sonatine726/zakojifarm_iotfieldsensor/Images/Products/1_8.PNG

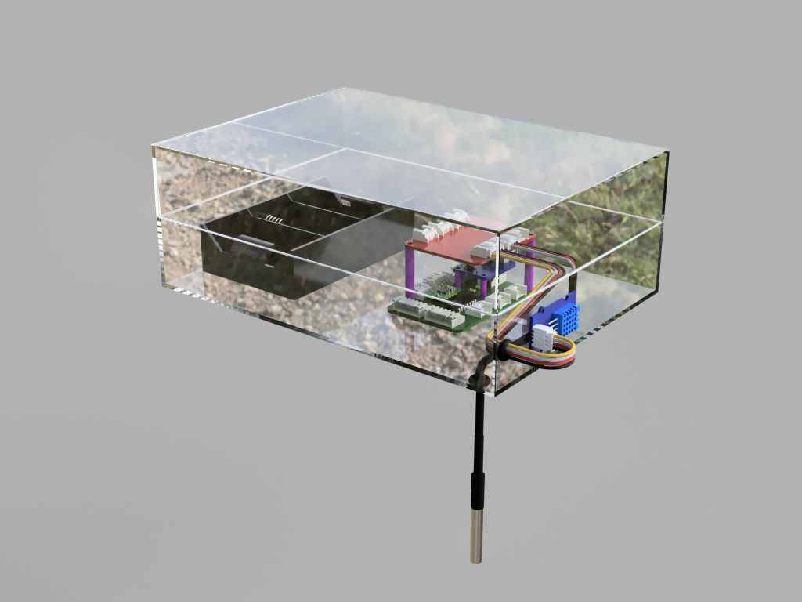
Images/Products/1_8.PNG
