sonatine726/zakojifarm_iotfieldsensor/Images/Products/2_6.PNG

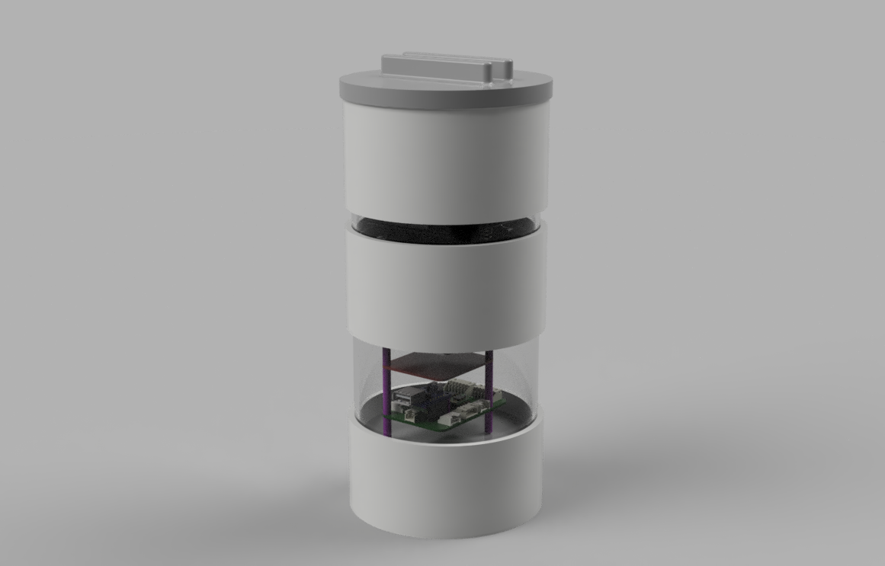
Images/Products/2_6.PNG
