sonatine726/zakojifarm_iotfieldsensor/Images/Products/2_9.jpg

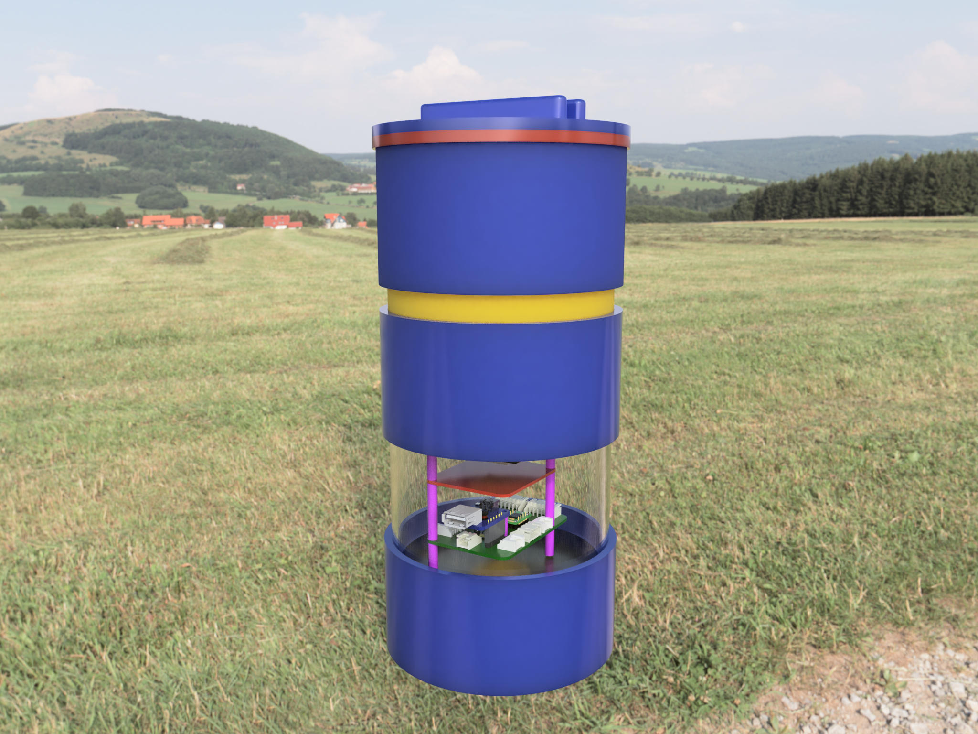
Images/Products/2_9.jpg
