sonatine726/zakojifarm_iotfieldsensor/Images/Products/4_1.PNG

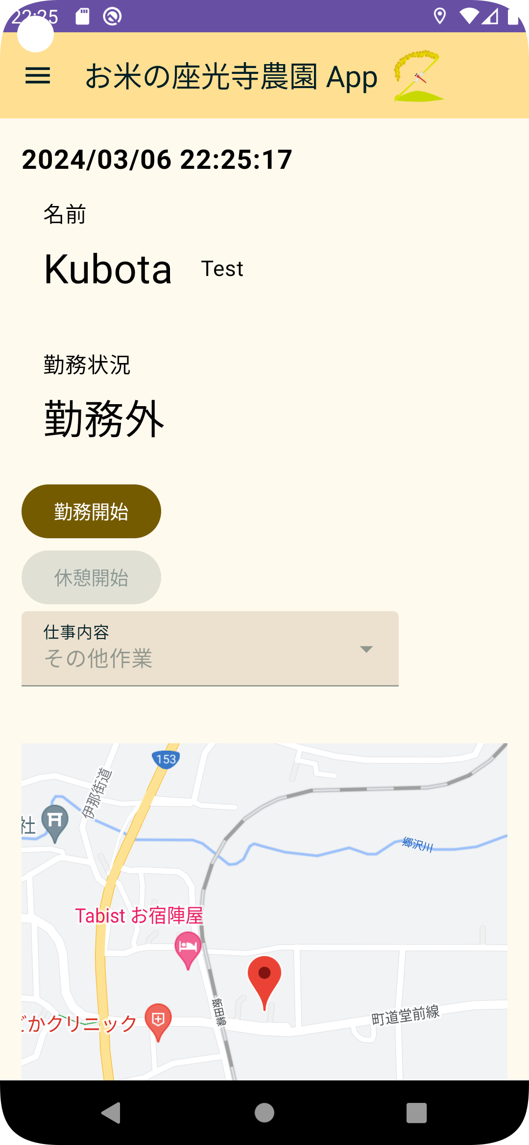
Images/Products/4_1.PNG
