sonatine726/zakojifarm_iotfieldsensor/Images/Products/4_2.PNG

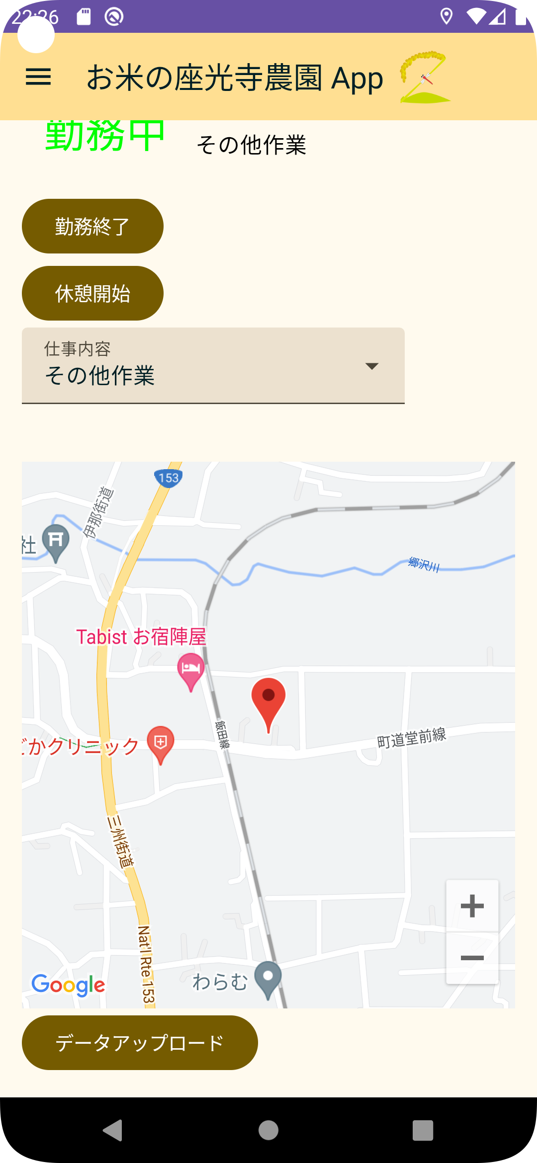
Images/Products/4_2.PNG
