sonatine726/zakojifarm_iotfieldsensor/Images/Products/5_1.jpg

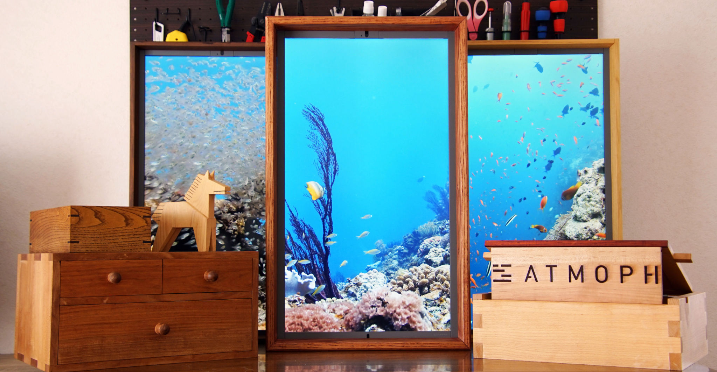
Images/Products/5_1.jpg
