sonatine726/zakojifarm_iotfieldsensor/Images/Products/5_2.jpg

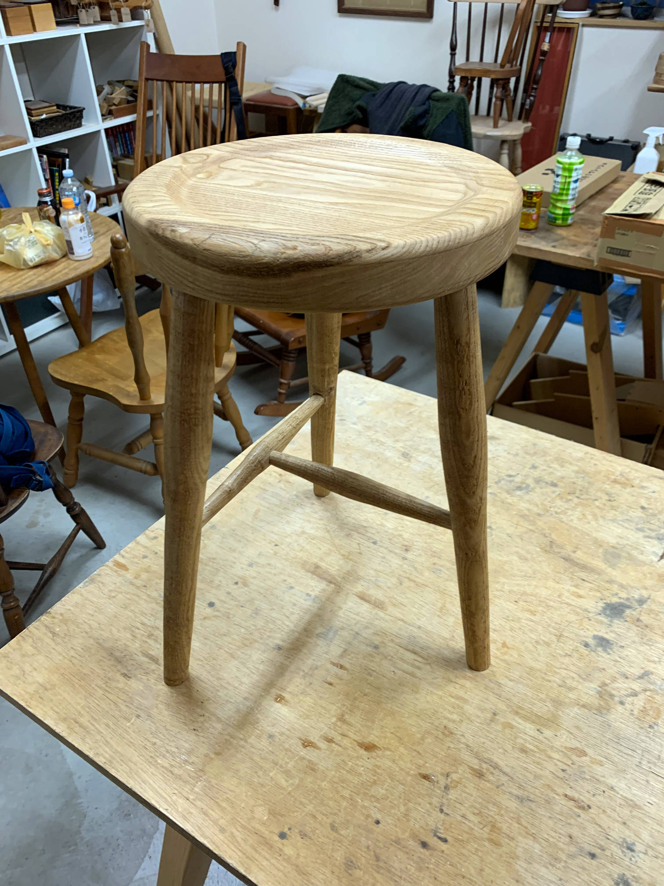
Images/Products/5_2.jpg
