sonatine726/zakojifarm_iotfieldsensor/Pcb/SensorToAmbient/SensorToAmbientPcb.png

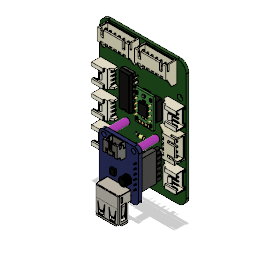
Pcb/SensorToAmbient/SensorToAmbientPcb.png
